BaykaI/DPAA/docs/img/01_steering.png

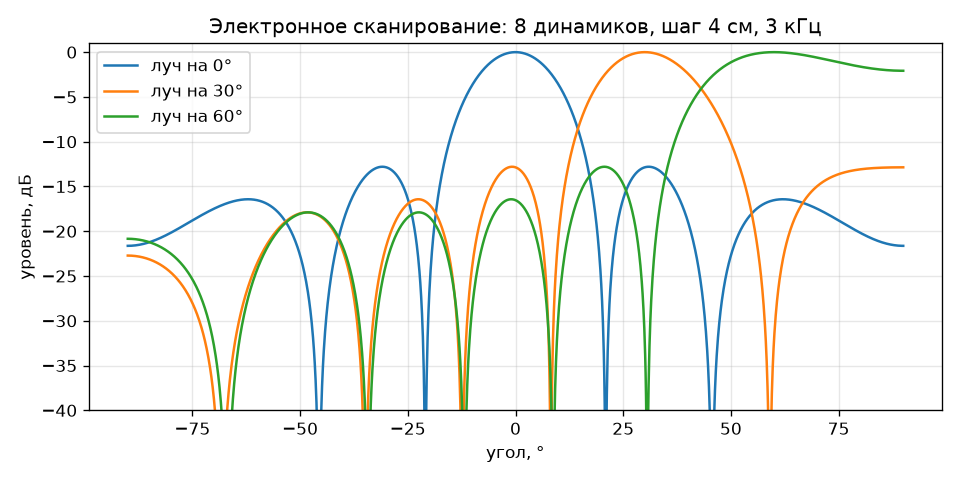
docs/img/01_steering.png
