BaykaI/DPAA/docs/img/structure.png

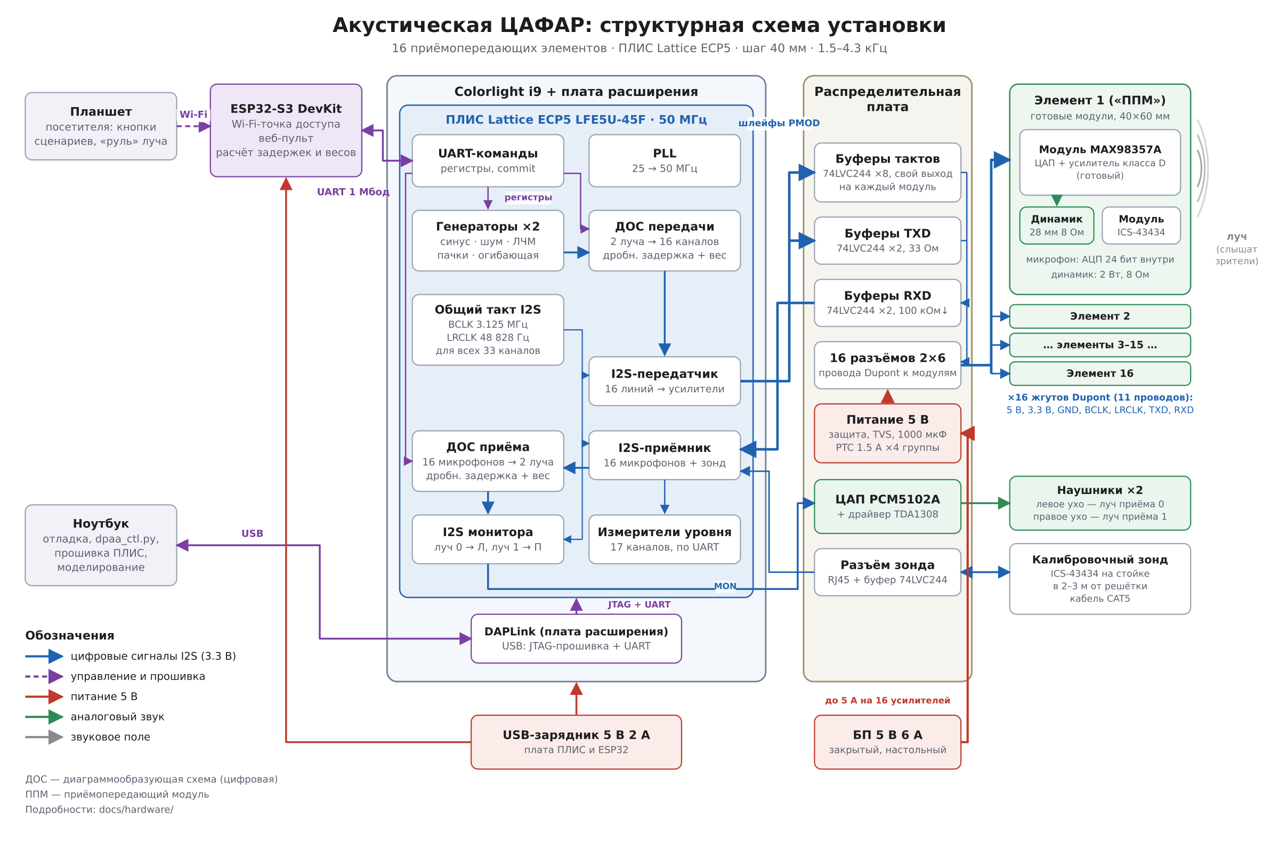
docs/img/structure.png
