BaykaI/DPAA/firmware/esp32/src/web_page.h

// Сгенерировано tools/embed_web.py из web/index.html — не редактировать вручную.
#pragma once
#include <stddef.h>
#include <stdint.h>

// 20629 байт страницы, 7227 байт в gzip
static const uint8_t WEB_PAGE_GZ[] = {
  0x1f, 0x8b, 0x08, 0x00, 0x00, 0x00, 0x00, 0x00, 0x02, 0x03, 0xc5, 0x5c, 0x7b, 0x6f, 0x1b, 0xd7, 0x95, 0xff, 0x5f, 0x9f,
  0xe2, 0x66, 0xdc, 0x06, 0xc3, 0x98, 0xa4, 0x38, 0xa4, 0x25, 0xcb, 0xa4, 0xe4, 0x6c, 0xe2, 0xa6, 0x88, 0x81, 0x6e, 0x6a,
  0x44, 0x09, 0x92, 0x85, 0xa1, 0x2d, 0x86, 0x9c, 0x21, 0x39, 0x15, 0x39, 0x33, 0x99, 0x19, 0x8a, 0x52, 0x54, 0x01, 0x76,
  0xbc, 0xad, 0xb3, 0x48, 0x5a, 0xf7, 0x85, 0xed, 0x6e, 0xbb, 0xd8, 0xb4, 0xfb, 0xe8, 0x16, 0x58, 0x14, 0xd0, 0x3a, 0x51,
  0xac, 0xf8, 0xa1, 0x00, 0xf9, 0x04, 0xd4, 0x57, 0xc8, 0x27, 0xd9, 0xdf, 0x39, 0xf7, 0xde, 0x79, 0x90, 0x23, 0x45, 0xe9,
  0x66, 0xb1, 0x4e, 0x2c, 0x0d, 0xef, 0x3d, 0xf7, 0x9e, 0x73, 0xcf, 0xfb, 0x9c, 0x3b, 0xf4, 0xfa, 0x73, 0x4e, 0xd0, 0x4b,
  0xf6, 0x42, 0x57, 0x0c, 0x93, 0xf1, 0xe8, 0xfa, 0xd2, 0x3a, 0xfd, 0x12, 0x23, 0xdb, 0x1f, 0x6c, 0x18, 0xd1, 0xc4, 0xa0,
  0x01, 0xd7, 0x76, 0xf0, 0x6b, 0xec, 0x26, 0xb6, 0xe8, 0x0d, 0xed, 0x28, 0x76, 0x93, 0x0d, 0x63, 0x92, 0xf4, 0x6b, 0x6b,
  0x86, 0x1e, 0xf6, 0xed, 0xb1, 0xbb, 0x61, 0xec, 0x78, 0xee, 0x34, 0x0c, 0xa2, 0xc4, 0x10, 0xbd, 0xc0, 0x4f, 0x5c, 0x1f,
  0x60, 0x53, 0xcf, 0x49, 0x86, 0x1b, 0x8e, 0xbb, 0xe3, 0xf5, 0xdc, 0x1a, 0x7f, 0xa8, 0x0a, 0xcf, 0xf7, 0x12, 0xcf, 0x1e,
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
  0x36, 0x89, 0xb3, 0xc4, 0xb6, 0xde, 0x24, 0x8a, 0x41, 0x47, 0x18, 0x78, 0xac, 0x00, 0x0b, 0xea, 0xa7, 0xe9, 0xa8, 0x07,
  0x85, 0x53, 0x28, 0xba, 0x1b, 0xa9, 0x02, 0x14, 0x8e, 0xd3, 0xd0, 0x7a, 0x4c, 0x74, 0x1c, 0x2c, 0x5d, 0x1a, 0xb8, 0x76,
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
};
static const size_t WEB_PAGE_GZ_LEN = 7227;
